RishabhMewada/MODULE-IHSC/Images/CAD-1.png

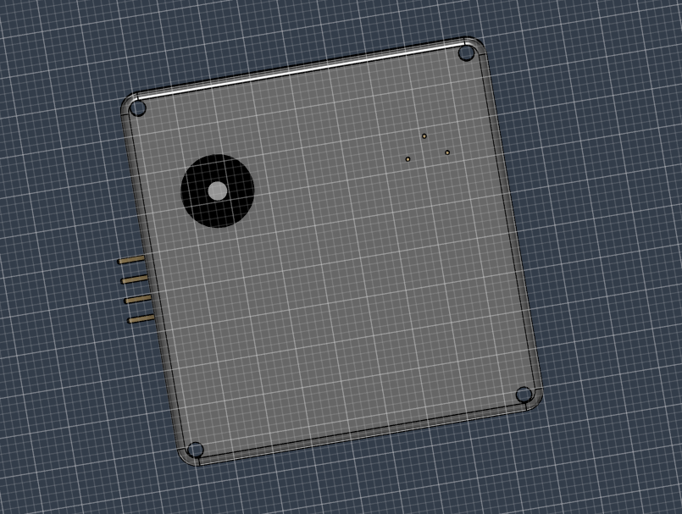
Images/CAD-1.png
