RishabhMewada/MODULE-IHSC/Images/CAD-2.png

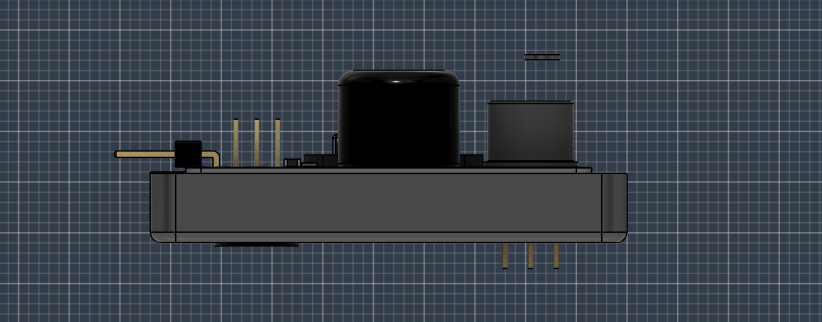
Images/CAD-2.png
