RishabhMewada/MODULE-IHSC/Images/Flowchart.png

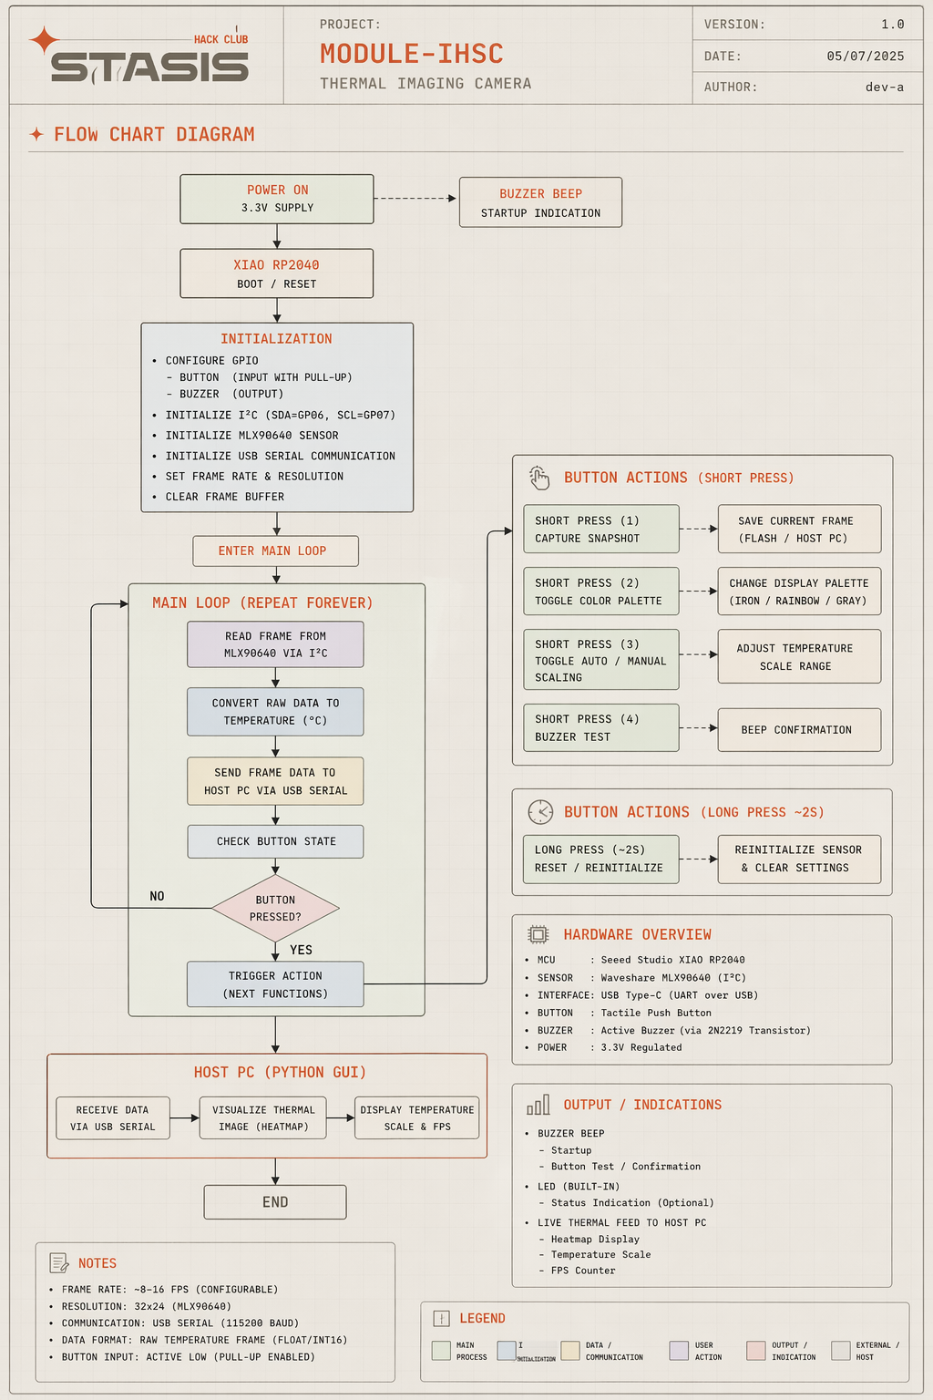
Images/Flowchart.png
