RishabhMewada/MODULE-IHSC/Images/PCB-3D-FRONT.png

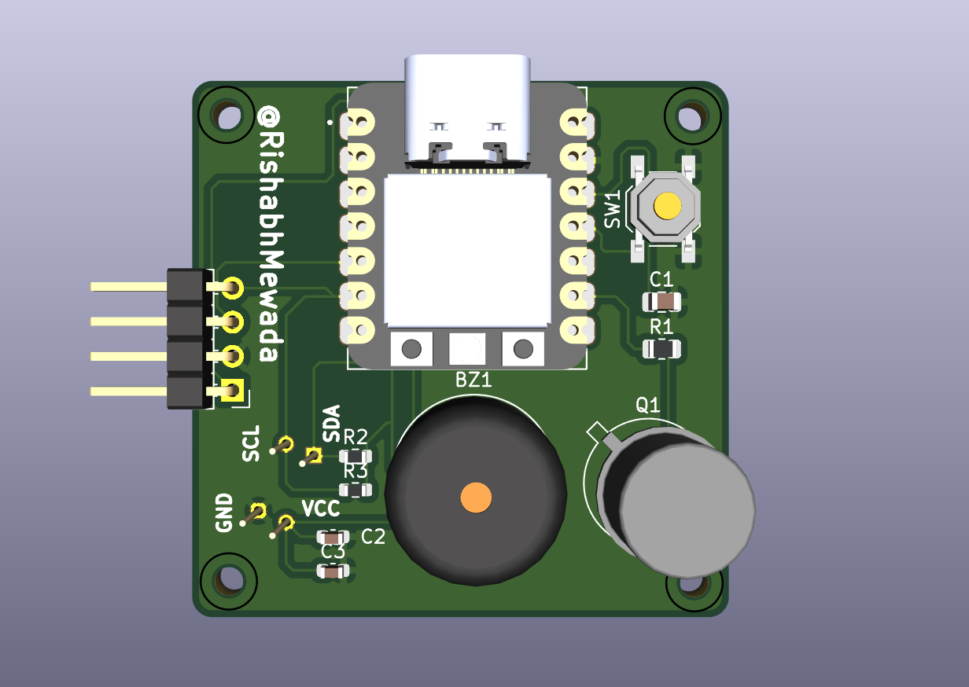
Images/PCB-3D-FRONT.png
