RishabhMewada/MODULE-IHSC/Images/PCB.png

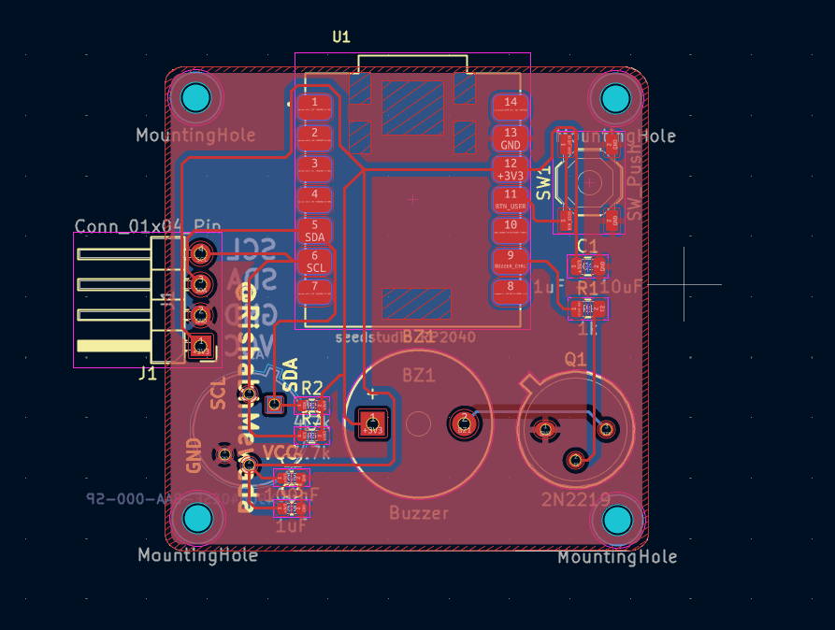
Images/PCB.png
